jotalac/crypto_viewer/code/display.cpp

#include "display.h"
#include "fonts/mono_small.h"
#include "fonts/mono_bold_50.h"
#include "fonts/mono_bold_60.h"
#include "fonts/mono_medium.h"
#include "utils.h"

TFT_eSPI tft = TFT_eSPI();

void draw_gradient(uint16_t color) {
  tft.fillRectVGradient(0, 0, tft.width(), tft.height(), TFT_BLACK, color);
}

void draw_curreny_title(String currency_title) {
  tft.setTextColor(LIGHT_GRAY, TFT_TRANSPARENT);
  
  tft.loadFont(mono_small);
  tft.drawString(currency_title , 20, 20);
  tft.unloadFont();
}

void draw_price(float price, bool centered) {
  std::string tempPriceString;  
  if (price == 0) {
    tempPriceString = "$ ...";
  } else {
    tempPriceString = "$ " + format_price(price);
  }
  String priceDisplay(tempPriceString.c_str());


  //the the right font size for the test length
  int maxWidth = tft.width() - 30;
  tft.loadFont(mono_bold_60);
  if (tft.textWidth(priceDisplay) > maxWidth) {
    tft.unloadFont();
    tft.loadFont(mono_bold_50);
    
    if (tft.textWidth(priceDisplay) > maxWidth) {
      tft.unloadFont();
      tft.loadFont(mono_medium);
    }
  }
  
  int y_location = centered ? tft.height() / 2 : 70;

  tft.setTextDatum(MC_DATUM);
  tft.setTextColor(TFT_WHITE, TFT_TRANSPARENT);
  tft.drawString(priceDisplay, tft.width() / 2, y_location);
  tft.unloadFont();

  tft.setTextDatum(TL_DATUM);
}



void draw_price_change(float price_change, String time_frame) {
  uint16_t bg_color;
  String display_string;

  //set the dispaly string
  if (price_change == 0.0f) {
    display_string = "...";
  } else {
    std::string temp = format_price_change(price_change, 2) + "%"; 
    display_string = String(temp.c_str());
  }

  //set the backgournd color
  if (price_change < 0) {
    bg_color = TFT_RED;
  } else {
    display_string = "+ " + display_string;
    bg_color = DARK_GREEN;
  }

  tft.loadFont(mono_medium);
  tft.setTextDatum(MC_DATUM);

  int padding = 10;
  int textWidth = tft.textWidth(display_string);
  int textHeight = tft.fontHeight();

  int x = tft.width() / 2;
  int y = 150;

  tft.fillRoundRect(x - textWidth / 2 - padding, y - textHeight / 2 - padding, textWidth + padding * 2, textHeight + padding * 2, 10, bg_color);
  tft.setTextColor(TFT_WHITE, TFT_TRANSPARENT);
  tft.drawString(display_string, x, y - 5);

  tft.unloadFont();

  //print the change time frame

  tft.loadFont(mono_small);
  tft.setTextColor(LIGHT_GRAY, TFT_TRANSPARENT);
  tft.drawString(time_frame, x, y + 40);
  tft.unloadFont();

  tft.setTextDatum(TL_DATUM); // Reset to default
}

void draw_ath_data(float ath_price, float ath_change) {
  tft.setTextDatum(MC_DATUM);
  tft.loadFont(mono_small);
  tft.setTextColor(TFT_WHITE, TFT_TRANSPARENT);

  // std::string change_formated = format_price_change(ath_change, 2) + "%";
  std::string price_format = format_price(ath_price);
  std::string change_format = format_price_change(ath_change, 2) + "%";

  tft.drawString("ATH: $ " + String(price_format.c_str()) + " | " + String(change_format.c_str()), tft.width() / 2, 220);
  // tft.drawString("ATH change: " + String(change_formated.c_str()), 150, 210);

  tft.unloadFont();
  tft.setTextDatum(TL_DATUM);
}


void render_screen(const CoinData &fetchedData, const GraphData &graph_data, const String time_frame) {
  
  // print_background(); // prints image
  uint16_t bg_color = fetchedData.price_change_percentage >= 0 ? DARK_YELLOW : TFT_RED;
  draw_gradient(bg_color);
  
  //display graph if selected
  if (should_display_graph()) {draw_graph(graph_data, fetchedData.price_change_percentage >= 0);}

  draw_curreny_title(String(fetchedData.symbol.c_str()));
  
  if (is_simple_layout()) {
    draw_price(fetchedData.price, true);
  } else {
    draw_price(fetchedData.price, false);
    draw_price_change(fetchedData.price_change_percentage, time_frame);
    draw_ath_data(fetchedData.ath_price, fetchedData.ath_percentage);

  }

}

void render_screen_clock() {
  static String last_time = "";
  String current_time = myTZ.dateTime("H:i");

  if (last_time == current_time) return;
  
  //draw background
  draw_gradient(DARK_BLUE);
  tft.setTextDatum(MC_DATUM);
  
  //draw timezone info
  tft.loadFont(mono_small);
  tft.setTextColor(LIGHT_GRAY, TFT_TRANSPARENT);
  tft.drawString(get_timezone(), tft.width() / 2, 50);
  tft.unloadFont();
  
  // draw the time 
  tft.loadFont(mono_bold_60);
  tft.setTextColor(TFT_WHITE, TFT_TRANSPARENT);
  tft.drawString(current_time, tft.width() / 2, tft.height() / 2);
  tft.unloadFont();
  tft.setTextDatum(TL_DATUM);  
  last_time = current_time;

}

void display_message(String message) {
  // tft.fillRect(0, 0, tft.width(), tft.height(), TFT_BLACK);
  draw_gradient(DARK_PURPLE);

  tft.setTextDatum(MC_DATUM);
  tft.loadFont(mono_small);
  tft.drawString(message, tft.width()/2, 100);
  tft.setTextDatum(TL_DATUM);

  tft.unloadFont();
}

void display_wifi_setup_message(String message) {
  draw_gradient(DARK_BLUE);

  
  tft.setTextColor(TFT_SKYBLUE, TFT_TRANSPARENT);
  
  tft.loadFont(mono_medium);
  tft.drawString(message, 20, 20);
  tft.unloadFont();
  
  tft.setTextColor(TFT_WHITE, TFT_TRANSPARENT);
  tft.loadFont(mono_small);

  tft.drawString("Connect to:", 20, 70);

  tft.drawString("SSID:", 30, 110);
  tft.drawString("crypto_display", 40, 130);
  
  tft.drawString("Password:", 30, 160);
  tft.drawString("crypto123", 40, 180);
  
  tft.unloadFont();
}


void draw_graph(GraphData graph_data, bool is_growing) {
  if (graph_data.data_count < 2) {
    Serial.println("No grapth data to display");
    return; 
  }

  // Layout Settings
  int graphX = 0; 
  int graphY = 50; 
  int graphW = 320; 
  int graphH = 240 - graphY - 20;
  int bottomY = graphY + graphH;

  uint16_t LINE_COLOR = is_growing ? GRAPH_LINE_GREEN : GRAPH_LINE_RED;
  uint16_t FILL_COLOR = is_growing ? GRAPH_FILL_GREEN : GRAPH_FILL_RED;

  float xSpacing = (float)graphW / (graph_data.data_count - 1);

  for (int i = 0; i < graph_data.data_count - 1; i++) {
    int x1 = graphX + (i * xSpacing);
    int x2 = graphX + ((i + 1) * xSpacing);
    
    float range = (graph_data.max_price - graph_data.min_price);
    if (range == 0) range = 1; 

    // Calculate Y positions
    int y1 = bottomY - ((graph_data.price_history[i] - graph_data.min_price) / range) * graphH;
    int y2 = bottomY - ((graph_data.price_history[i+1] - graph_data.min_price) / range) * graphH;

  
    // fill the space under the graph
    tft.fillTriangle(x1, y1, x2, y2, x1, tft.height(), FILL_COLOR);
    tft.fillTriangle(x1, tft.height(), x2, y2, x2, tft.height(), FILL_COLOR);

    // Draw the graph line
    tft.drawWideLine(x1, y1 , x2, y2, 5, LINE_COLOR, TFT_BLACK);


    // draw graph with verical lines
    // uint16_t line_color = y1 > y2 ? TFT_GREEN : TFT_RED;
    // tft.drawWideLine(x1, y1, x1, y2, xSpacing - 2, line_color);
    
  }
}
